Ya3in13/my-Lily58-keyboard/img/fol .jpg

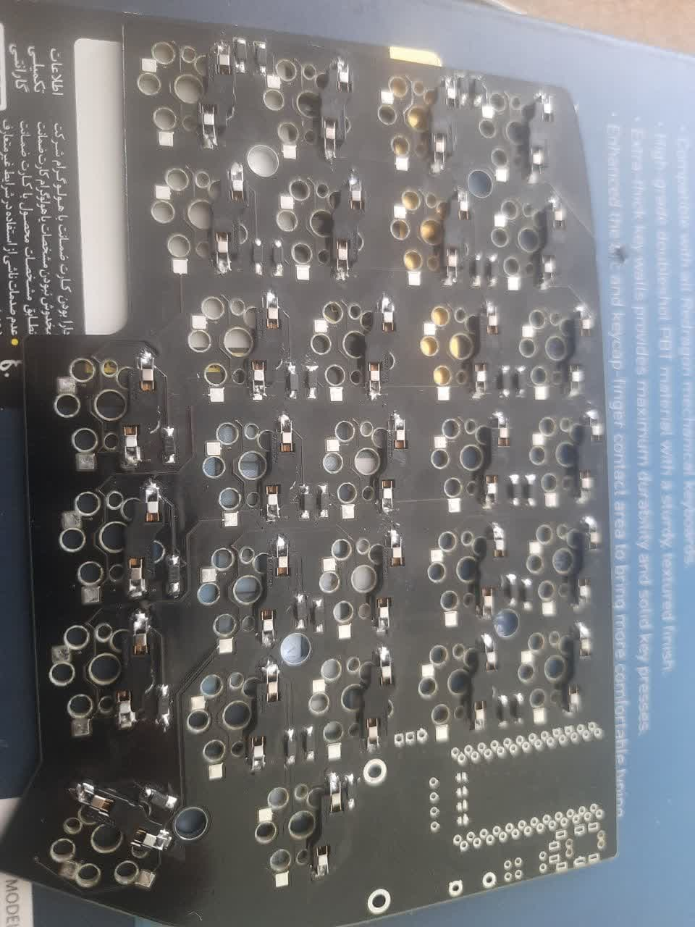
img/fol .jpg
