Ya3in13/my-Lily58-keyboard/img/kham.jpg

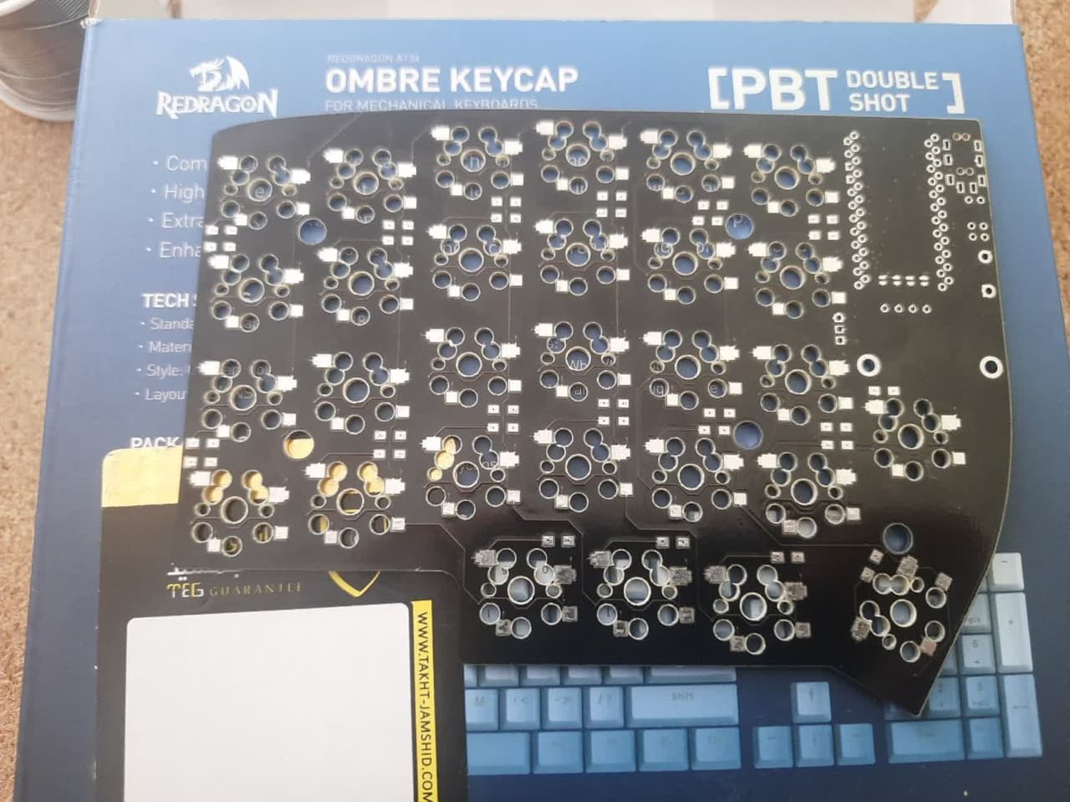
img/kham.jpg
