Ya3in13/my-Lily58-keyboard/img/micro.jpg

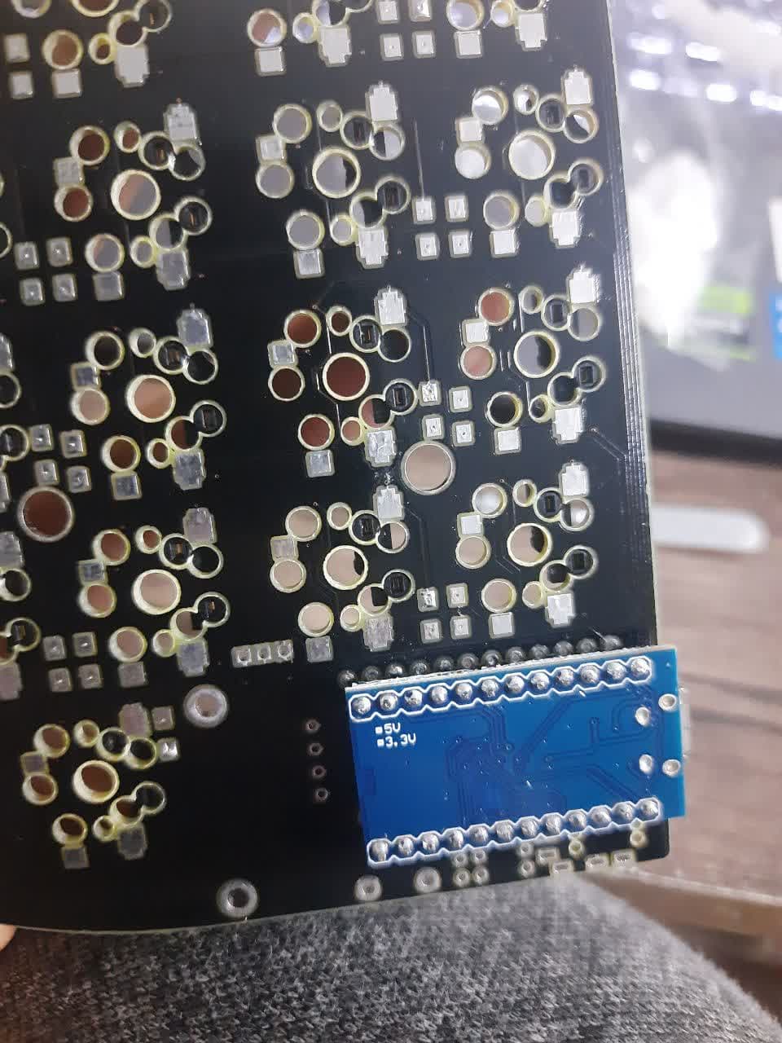
img/micro.jpg
