Ya3in13/my-Lily58-keyboard/img/sokt ha.jpg

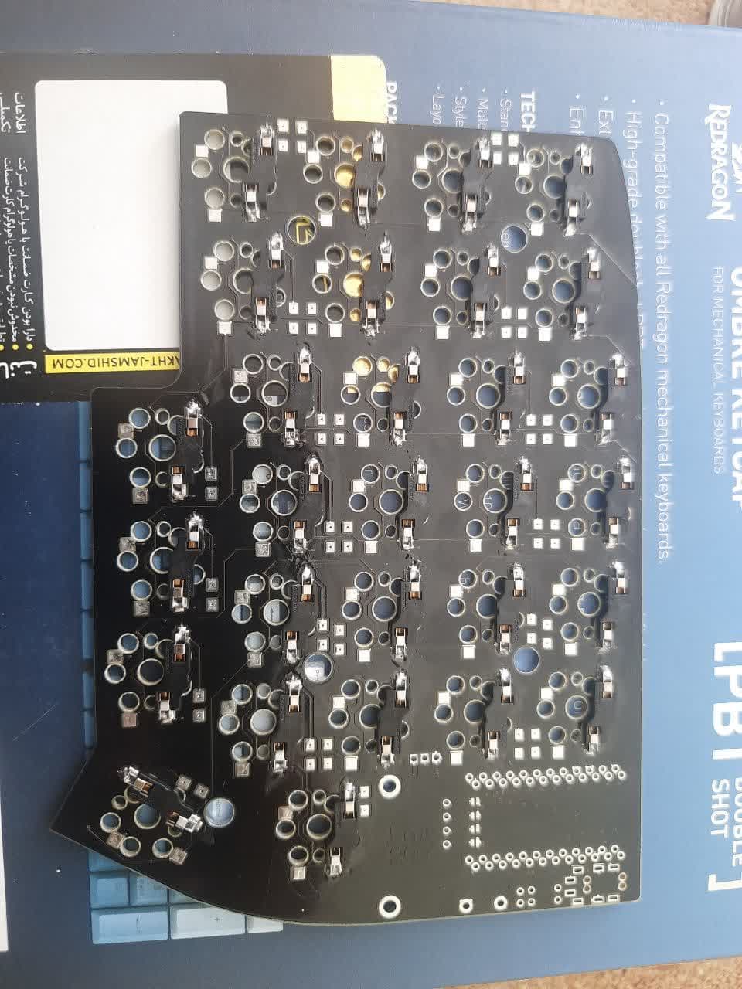
img/sokt ha.jpg
