Ya3in13/my-Lily58-keyboard/img/ki test.png

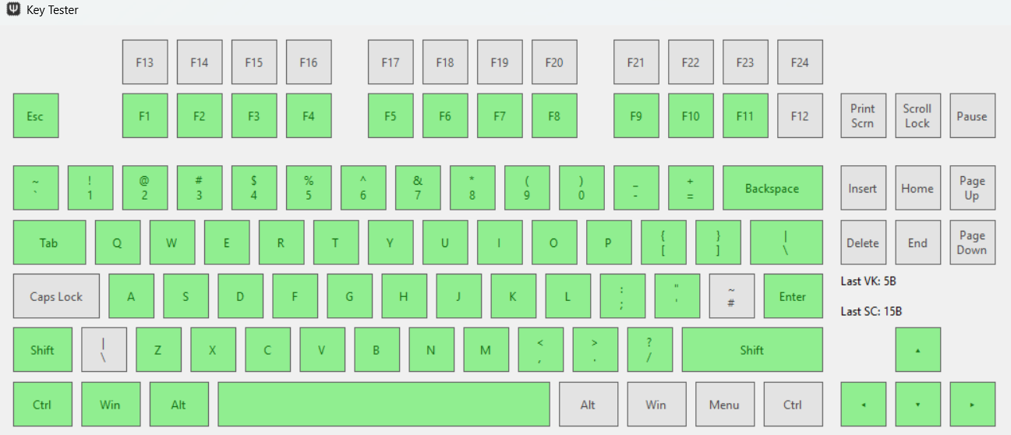
img/ki test.png
